JulienChoukroun/Arduino/Documentation/Boîte-Machine/BoiteMontee.jpg

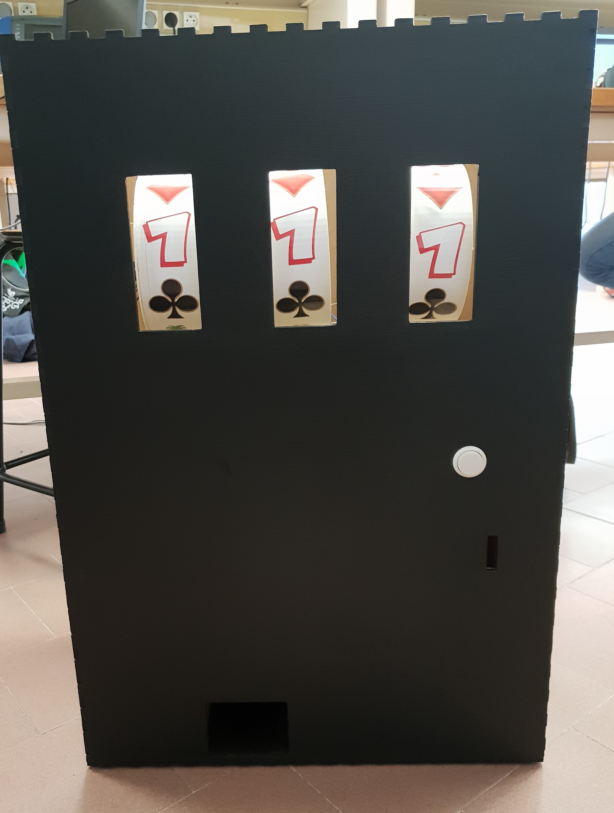
Documentation/Boîte-Machine/BoiteMontee.jpg
