JulienChoukroun/Arduino/Documentation/Boîte-Machine/InterieurBoite.jpg

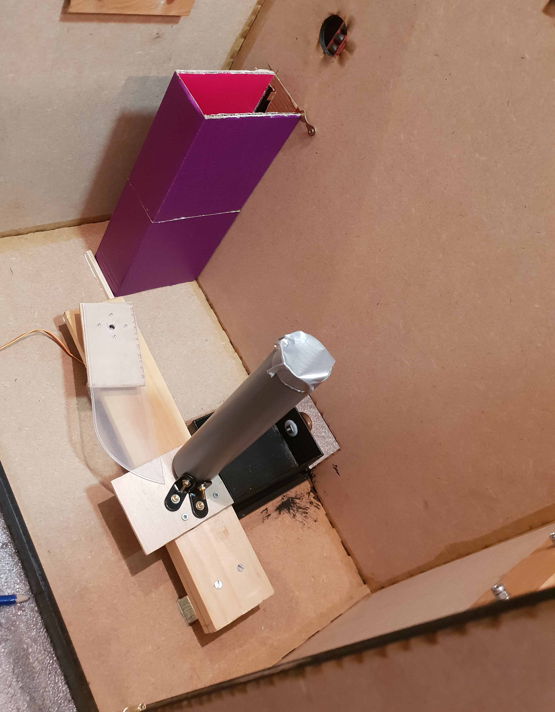
Documentation/Boîte-Machine/InterieurBoite.jpg
