JulienChoukroun/Arduino/Documentation/Boîte-Machine/machineASous.jpg

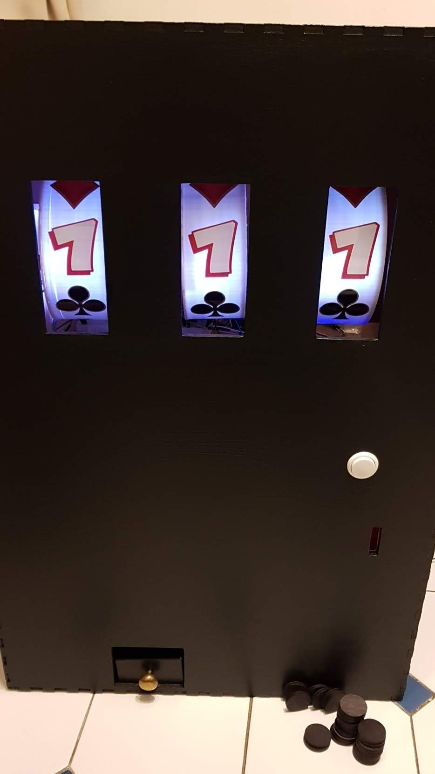
Documentation/Boîte-Machine/machineASous.jpg
