JulienChoukroun/Arduino/Documentation/Boîte-Machine/PorteBoite.jpg

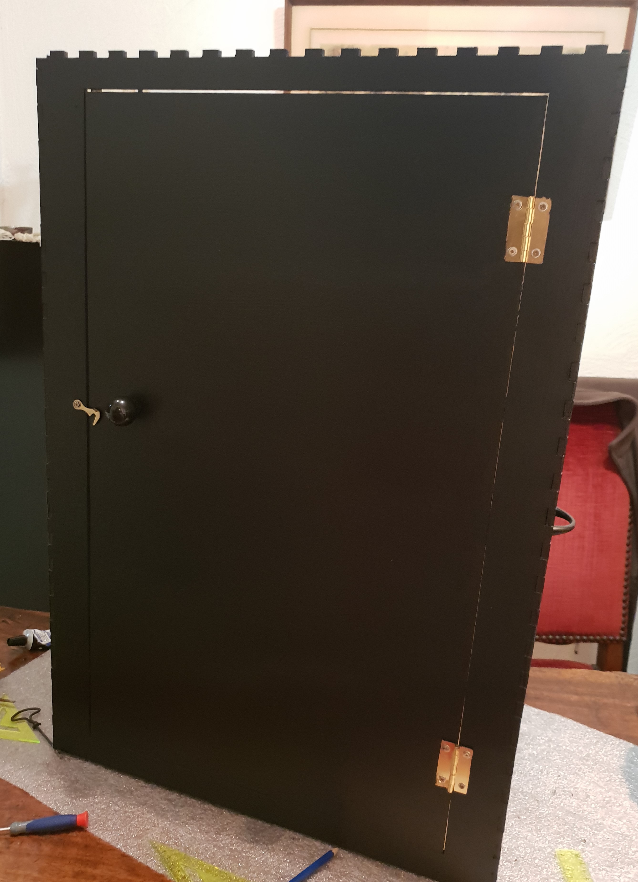
Documentation/Boîte-Machine/PorteBoite.jpg
