JulienChoukroun/Arduino/Documentation/Boîte-Machine/Projet machine à sous part1.jpg

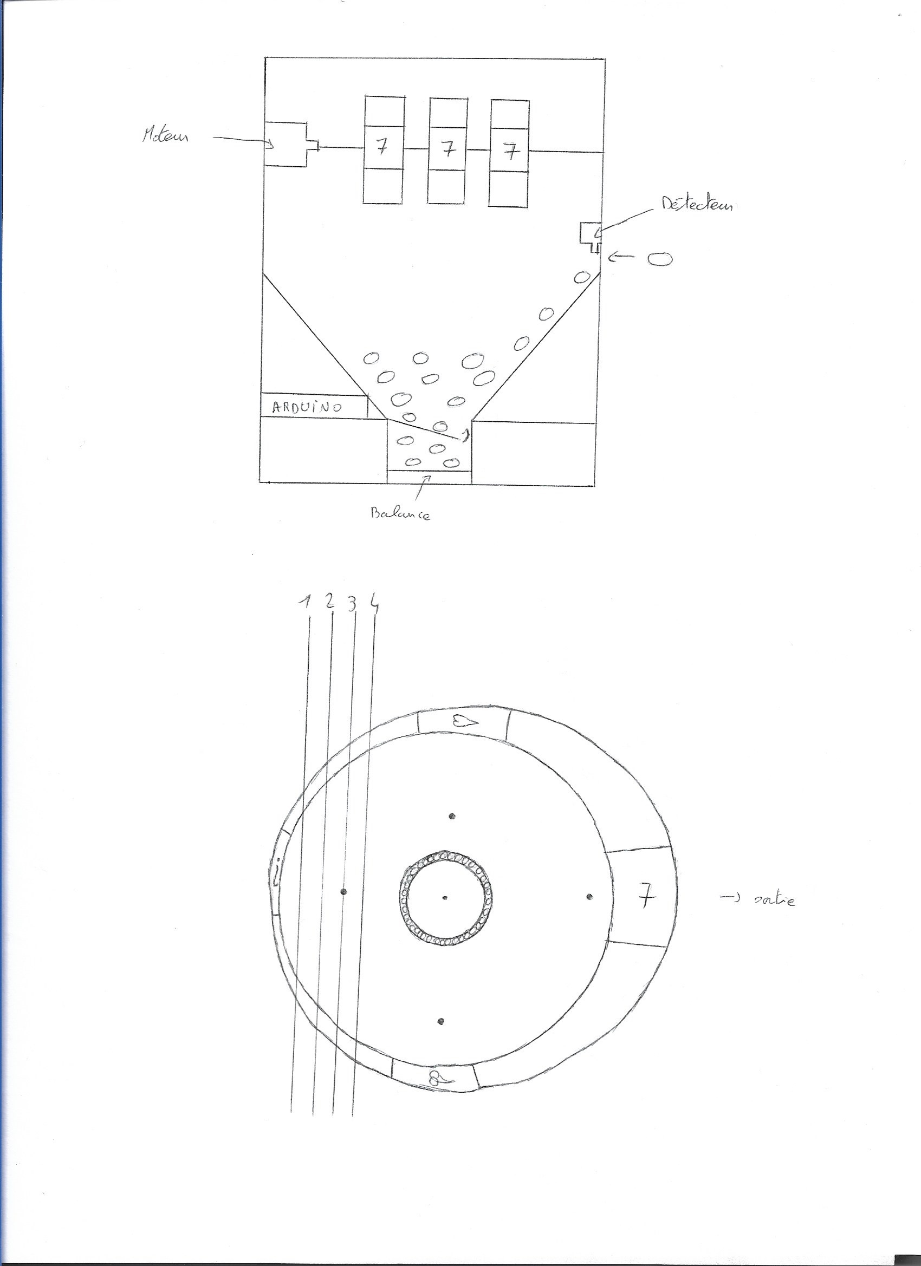
Documentation/Boîte-Machine/Projet machine à sous part1.jpg
