JulienChoukroun/Arduino/Documentation/Boîte-Machine/Projet machine à sous part2.jpg

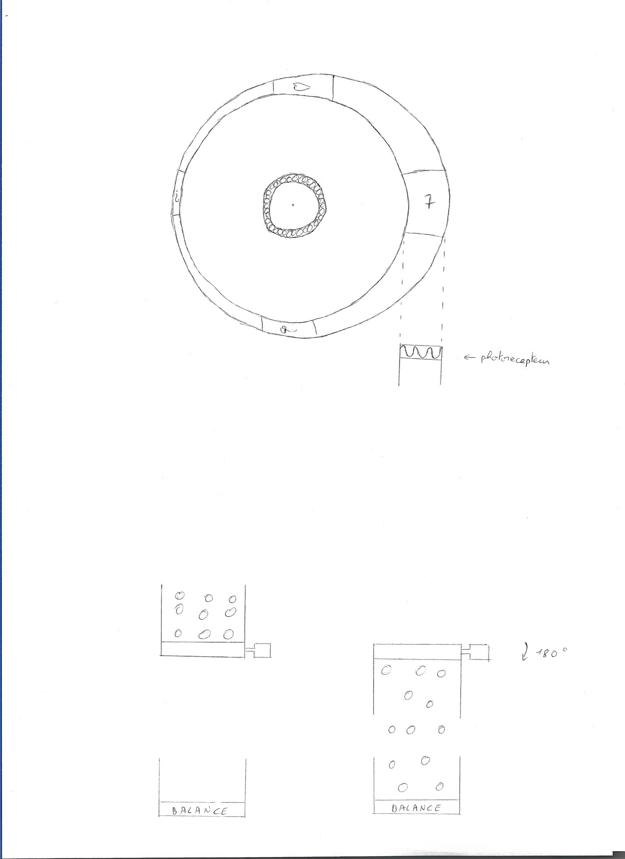
Documentation/Boîte-Machine/Projet machine à sous part2.jpg
