JulienChoukroun/Arduino/Documentation/Boîte-Machine/schémaMachine.jpg

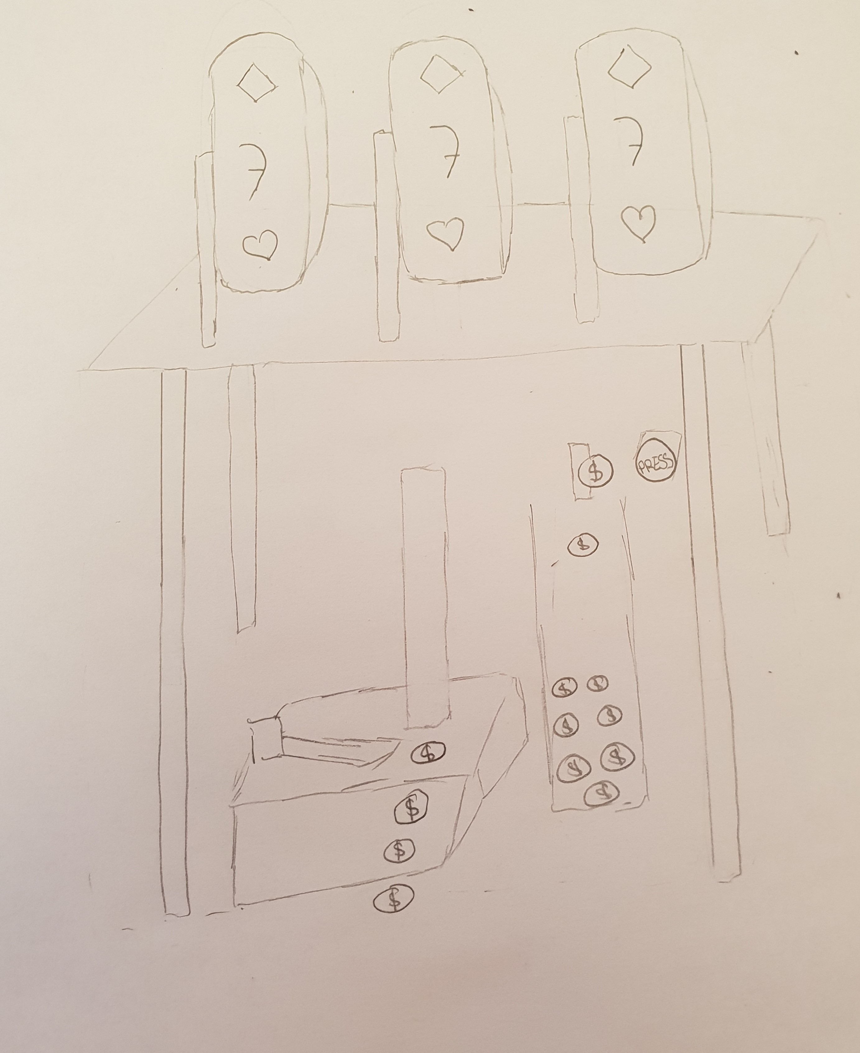
Documentation/Boîte-Machine/schémaMachine.jpg
