JulienChoukroun/Arduino/Documentation/DiagrammeGant/DiagrammeDeGanttPart1.PNG

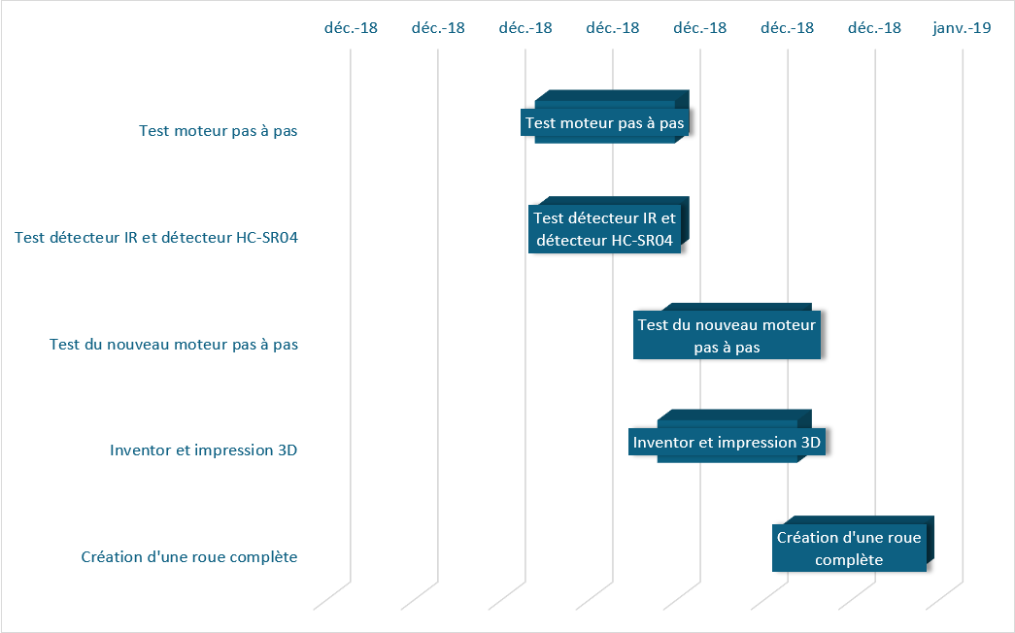
Documentation/DiagrammeGant/DiagrammeDeGanttPart1.PNG
