JulienChoukroun/Arduino/Documentation/DiagrammeGant/DiagrammeDeGanttPart2.PNG

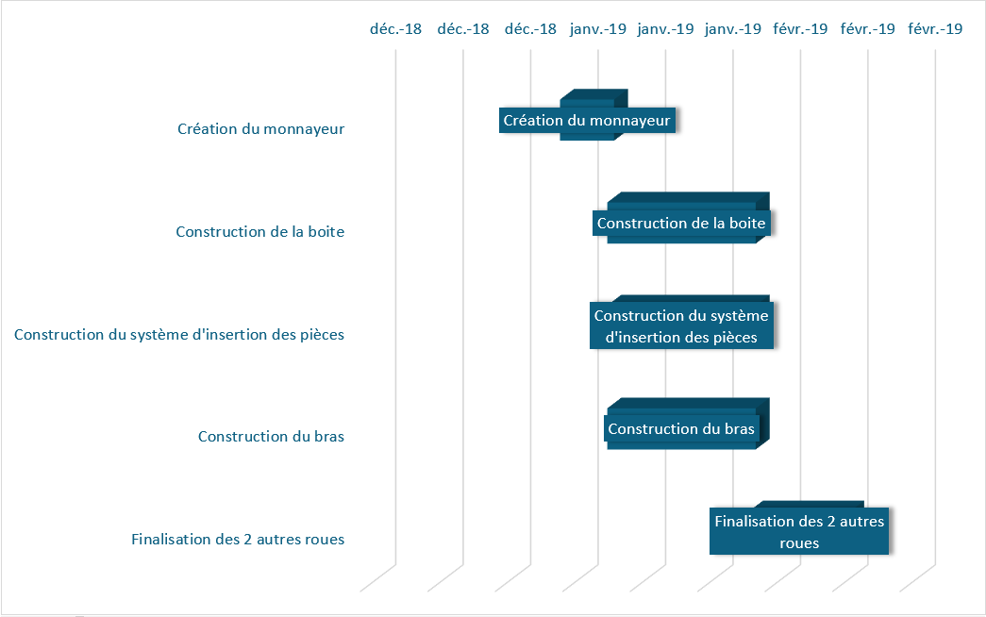
Documentation/DiagrammeGant/DiagrammeDeGanttPart2.PNG
