JulienChoukroun/Arduino/Documentation/DiagrammeGant/DiagrammeDeGanttPart3.PNG

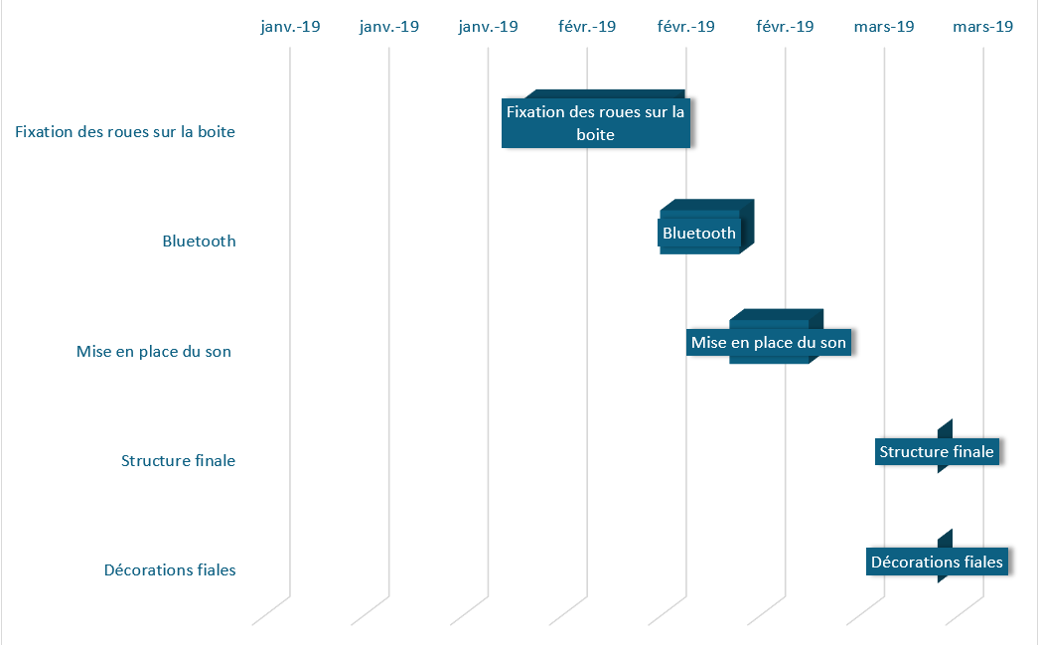
Documentation/DiagrammeGant/DiagrammeDeGanttPart3.PNG
