JulienChoukroun/Arduino/Documentation/DiagrammeGant/NouveauGantt1.PNG

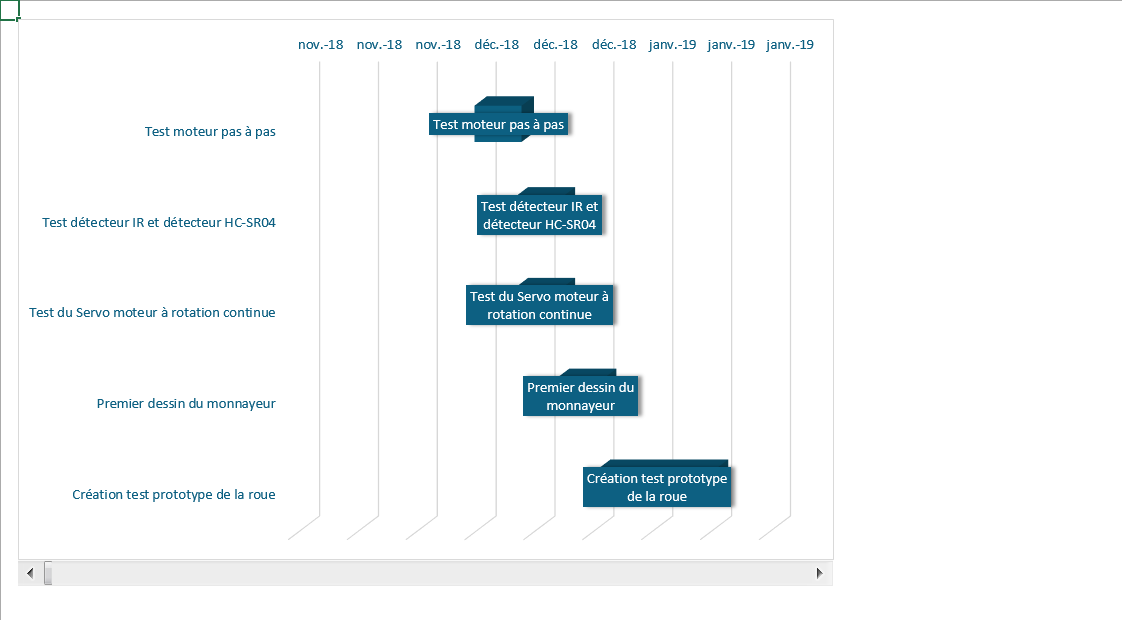
Documentation/DiagrammeGant/NouveauGantt1.PNG
