JulienChoukroun/Arduino/Documentation/DiagrammeGant/NouveauGantt2.PNG

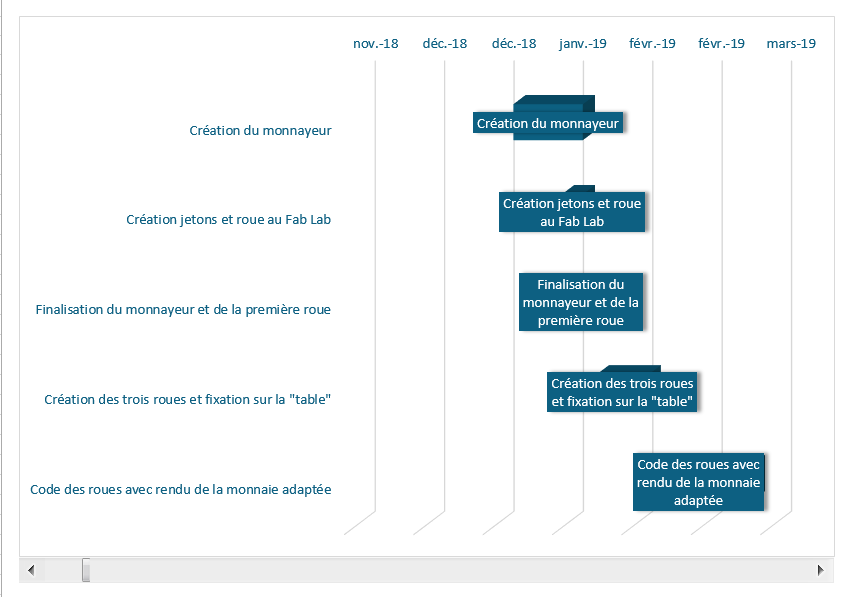
Documentation/DiagrammeGant/NouveauGantt2.PNG
