JulienChoukroun/Arduino/Documentation/DiagrammeGant/NouveauGantt3.PNG

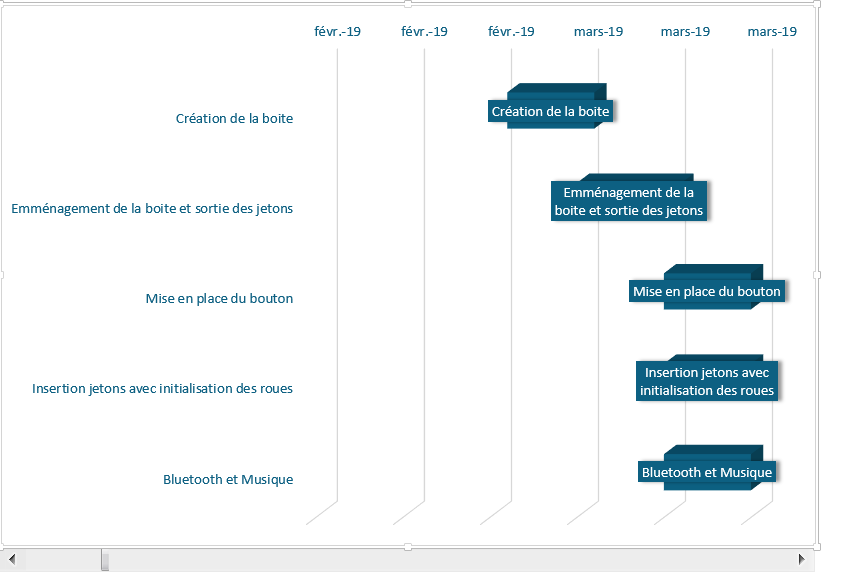
Documentation/DiagrammeGant/NouveauGantt3.PNG
