JulienChoukroun/Arduino/Documentation/liste_planification_part1.jpg

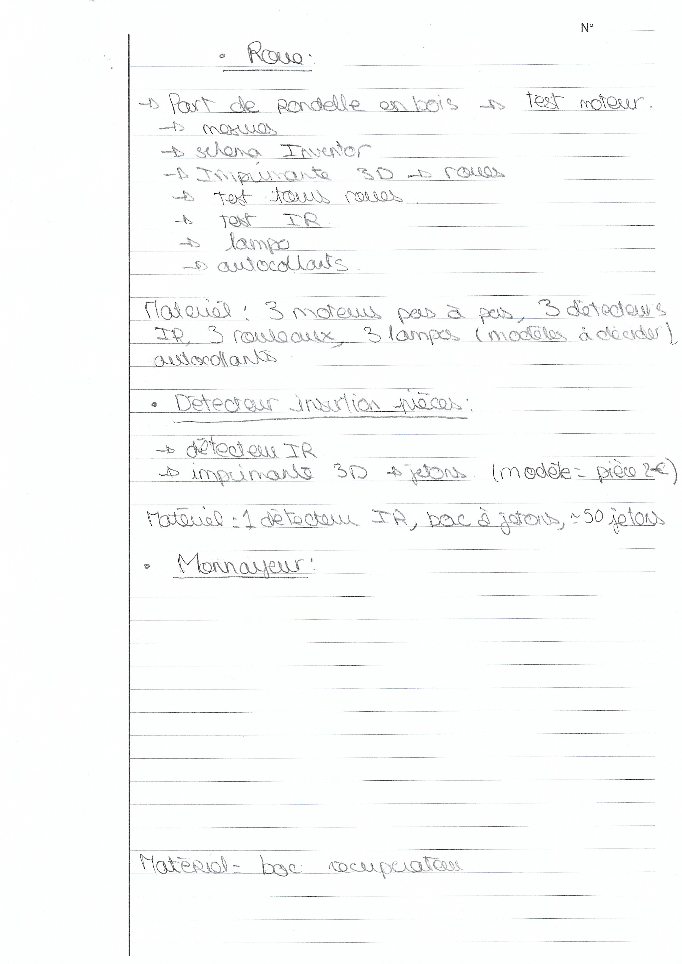
Documentation/liste_planification_part1.jpg
