JulienChoukroun/Arduino/Documentation/liste_planification_part2.jpg

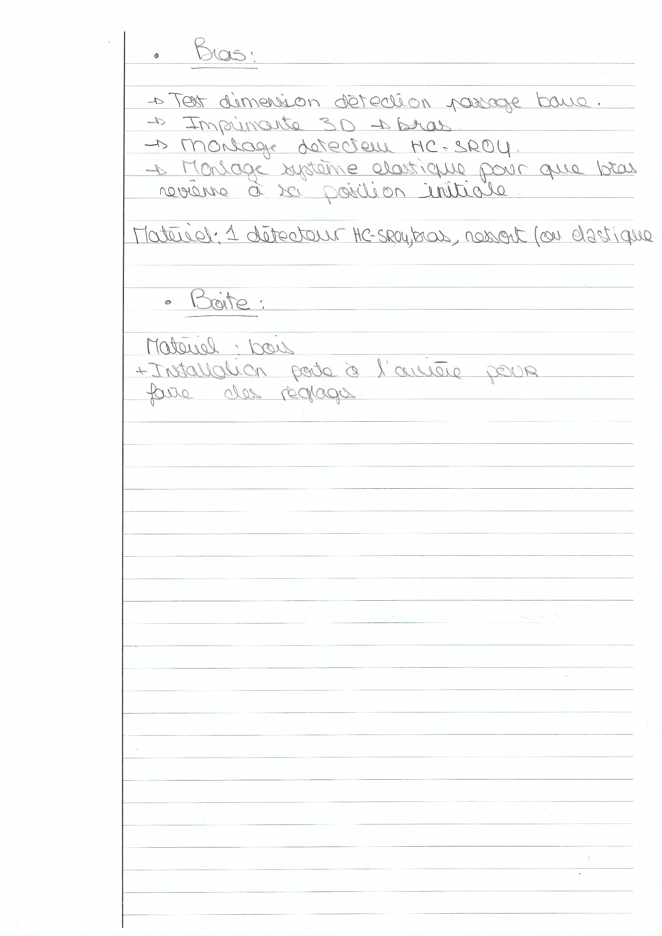
Documentation/liste_planification_part2.jpg
