JulienChoukroun/Arduino/Documentation/Monnayeur/DessinMonnayeur.jpg

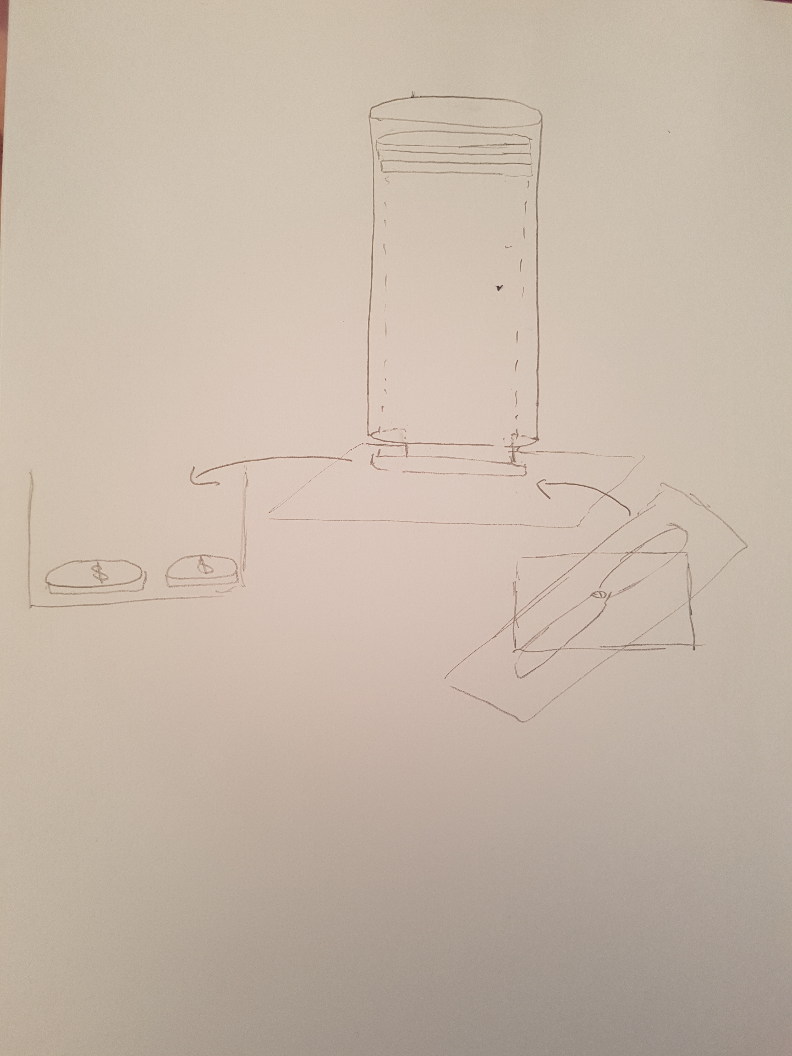
Documentation/Monnayeur/DessinMonnayeur.jpg
