JulienChoukroun/Arduino/Documentation/Monnayeur/nouveauMonnayeur.jpg

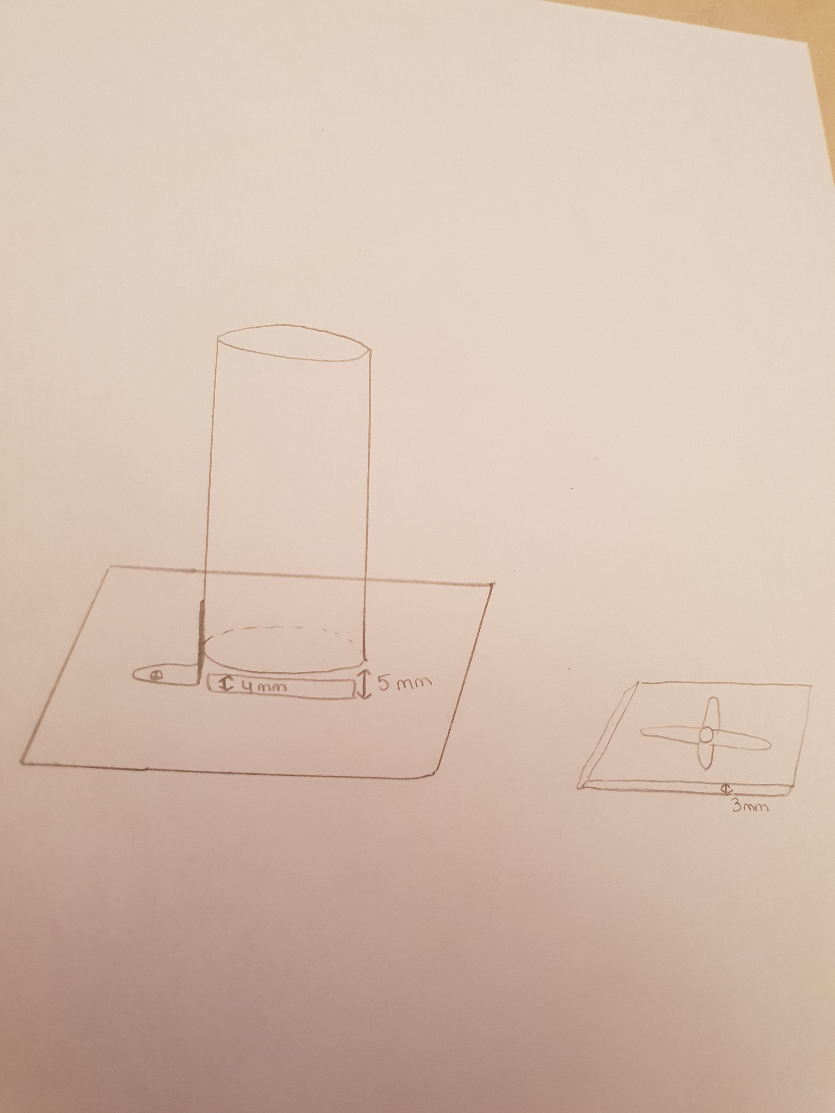
Documentation/Monnayeur/nouveauMonnayeur.jpg
