JulienChoukroun/Arduino/Documentation/Roue/moteurtest.jpg

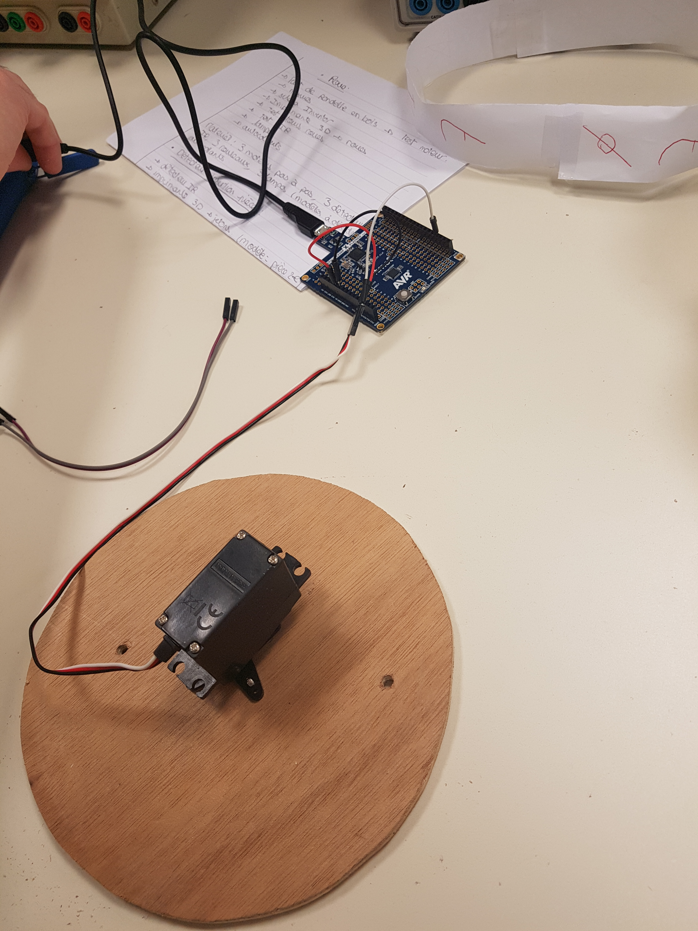
Documentation/Roue/moteurtest.jpg
