JulienChoukroun/Arduino/Documentation/Roue/roueAutocollant.jpg

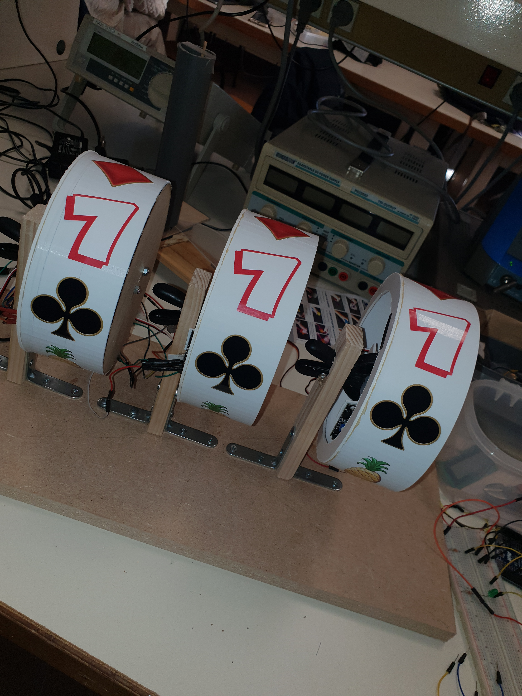
Documentation/Roue/roueAutocollant.jpg
