JulienChoukroun/Arduino/Documentation/Roue/RoueEclairée.jpg

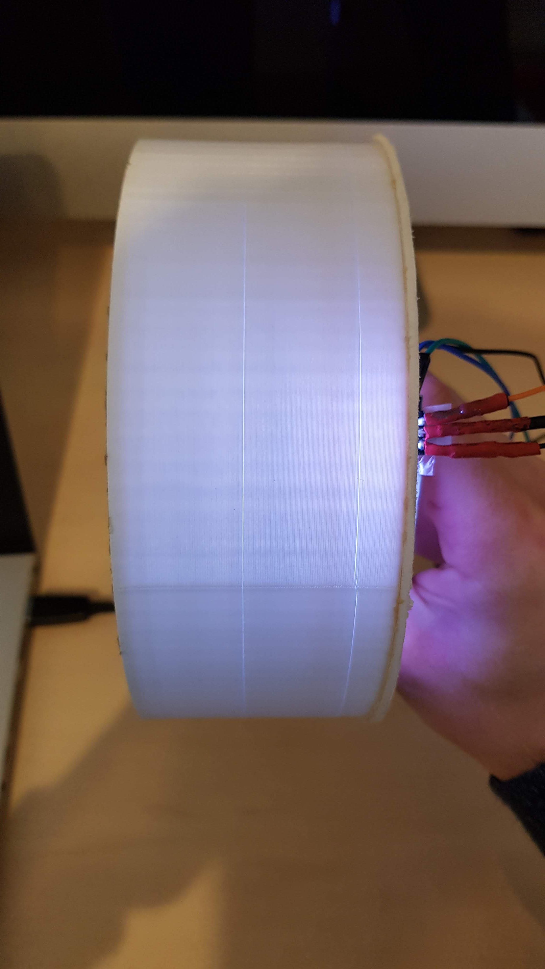
Documentation/Roue/RoueEclairée.jpg
