JulienChoukroun/Arduino/Documentation/Roue/supportFixationRoues.jpeg

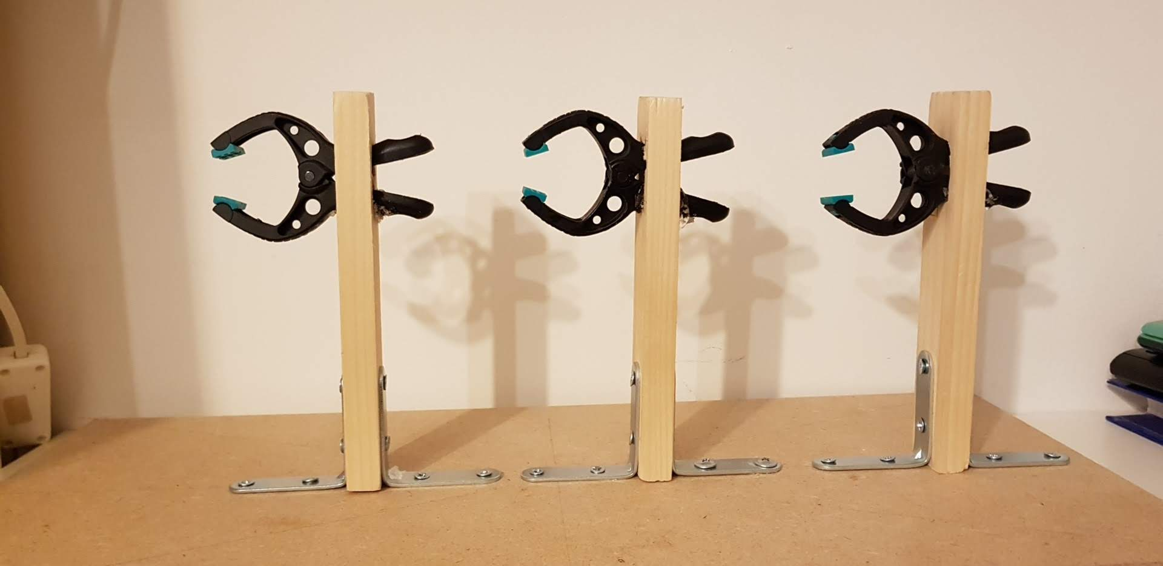
Documentation/Roue/supportFixationRoues.jpeg
