JulienChoukroun/Arduino/Documentation/Roue/roueAssembléeIntérieur.jpg

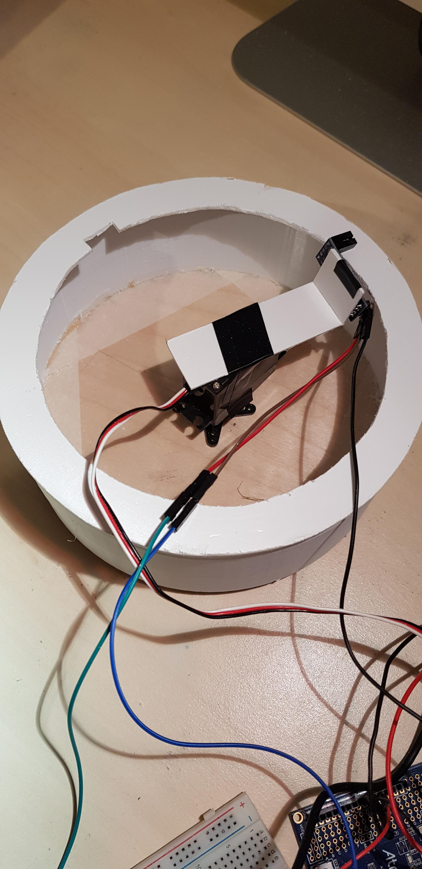
Documentation/Roue/roueAssembléeIntérieur.jpg
