JulienChoukroun/Arduino/Documentation/Roue/premiereroue.jpg

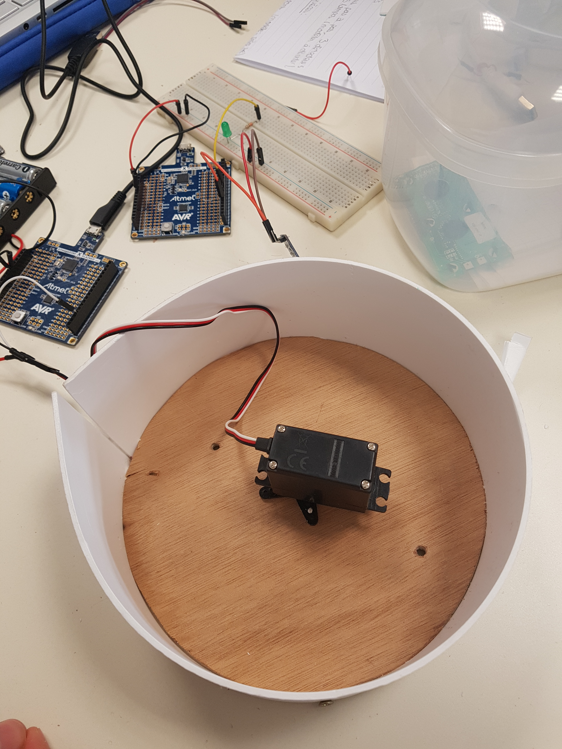
Documentation/Roue/premiereroue.jpg
